phongnickchinh/sendove-box/sendlove_enclosure/breadcat/huong_dan/H02_giao_dien.png

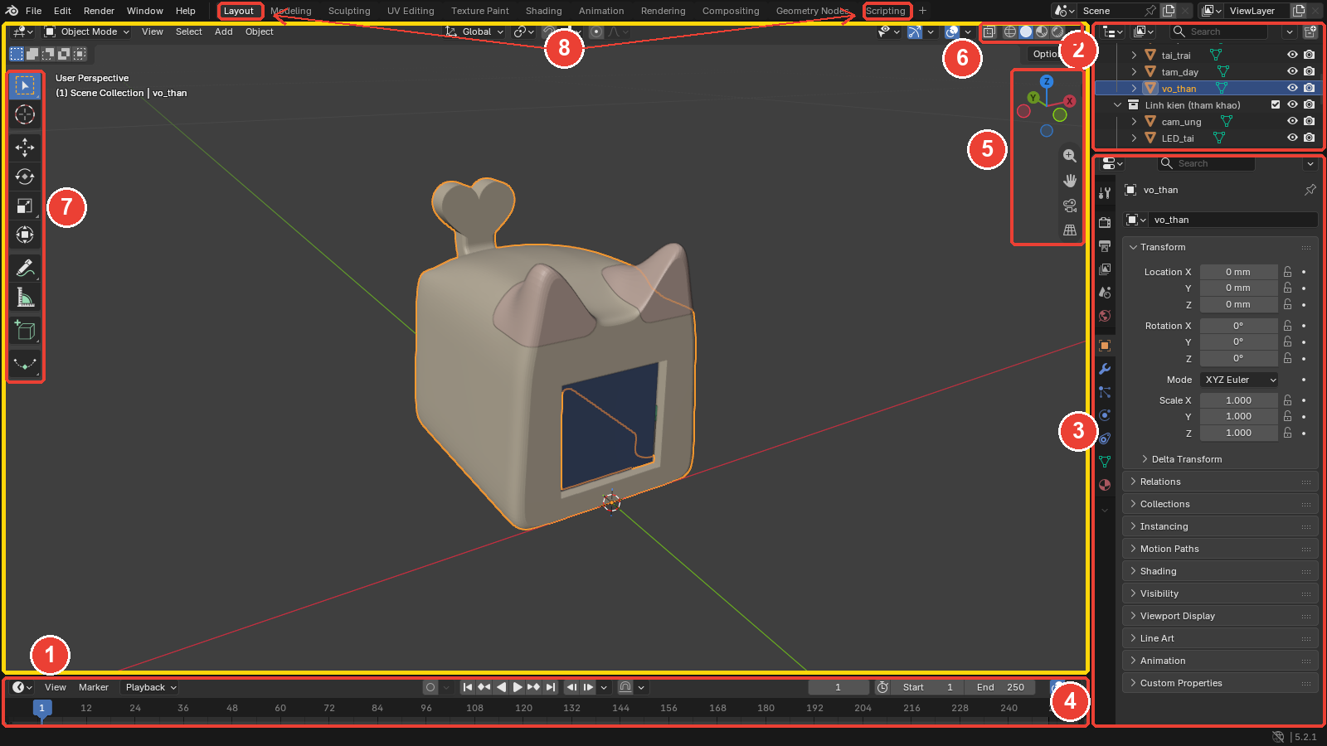
sendlove_enclosure/breadcat/huong_dan/H02_giao_dien.png
