phongnickchinh/sendove-box/sendlove_enclosure/breadcat/huong_dan/H03_gizmo.png

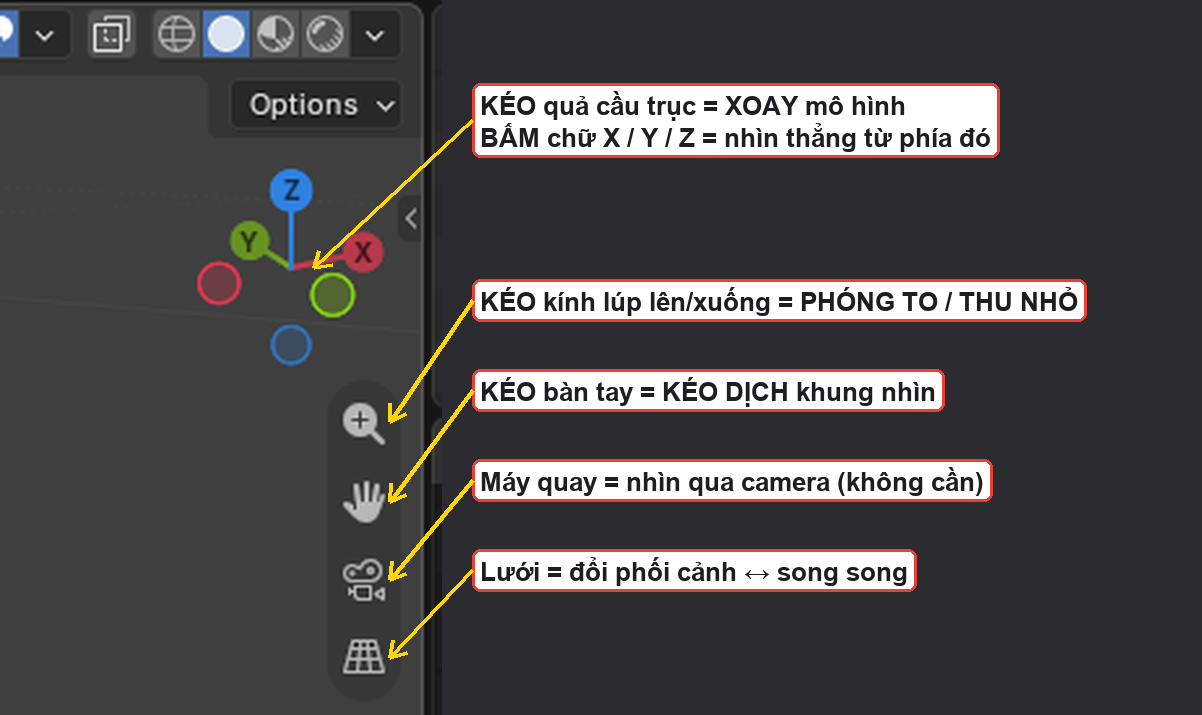
sendlove_enclosure/breadcat/huong_dan/H03_gizmo.png
