phongnickchinh/sendove-box/sendlove_enclosure/breadcat/huong_dan/H04_chuot.png

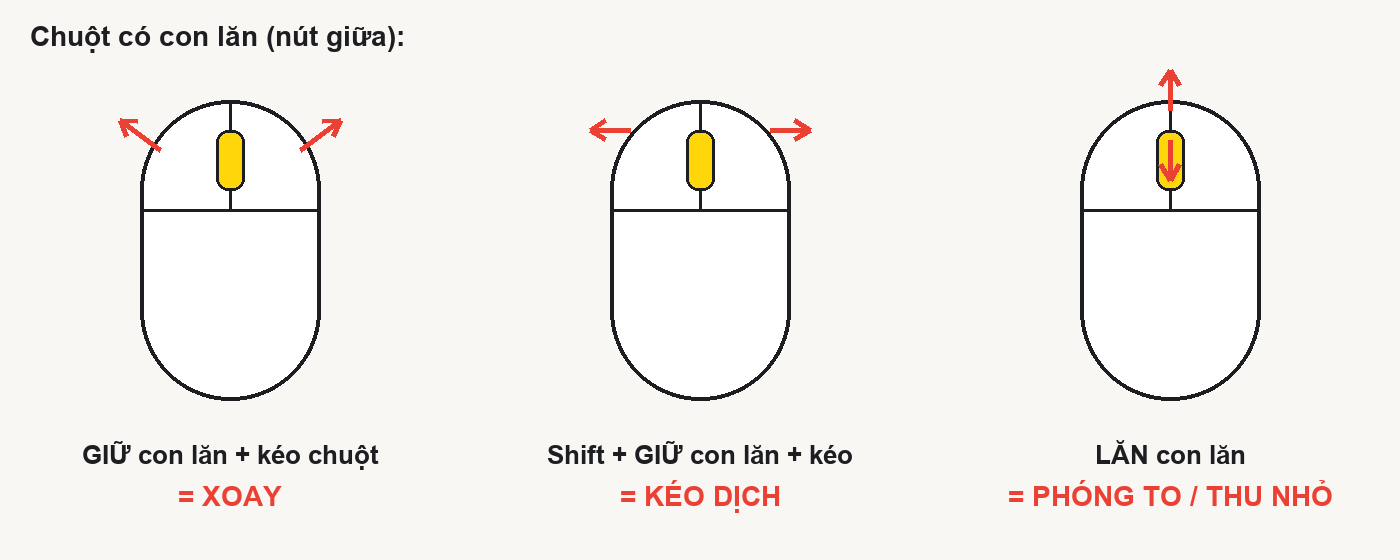
sendlove_enclosure/breadcat/huong_dan/H04_chuot.png
