phongnickchinh/sendove-box/sendlove_enclosure/breadcat/huong_dan/H05_prefs_input.png

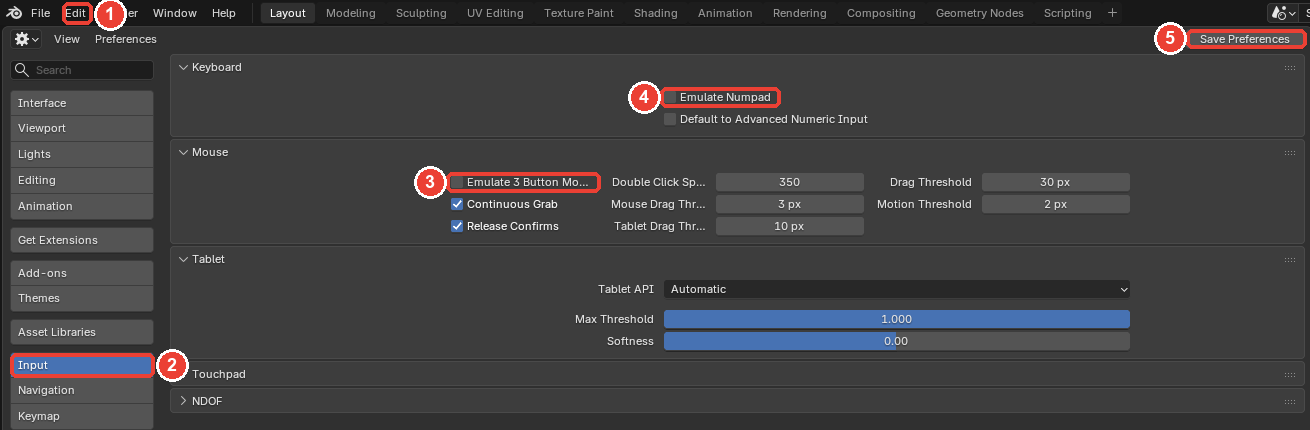
sendlove_enclosure/breadcat/huong_dan/H05_prefs_input.png
