phongnickchinh/sendove-box/sendlove_enclosure/breadcat/huong_dan/H07_menu_view.png

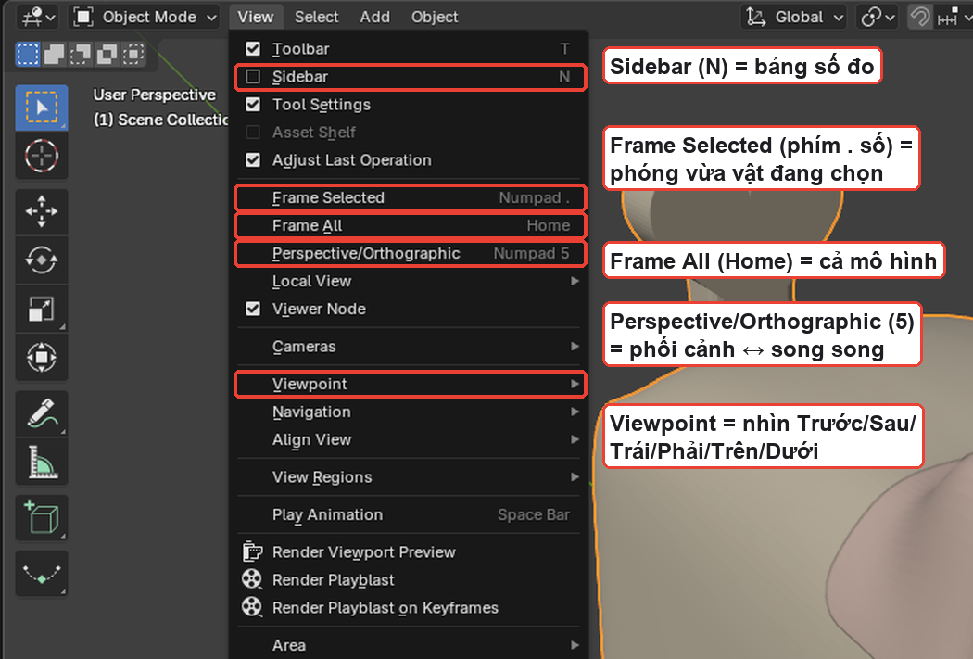
sendlove_enclosure/breadcat/huong_dan/H07_menu_view.png
