phongnickchinh/sendove-box/sendlove_enclosure/breadcat/huong_dan/H08_goc_chuan.png

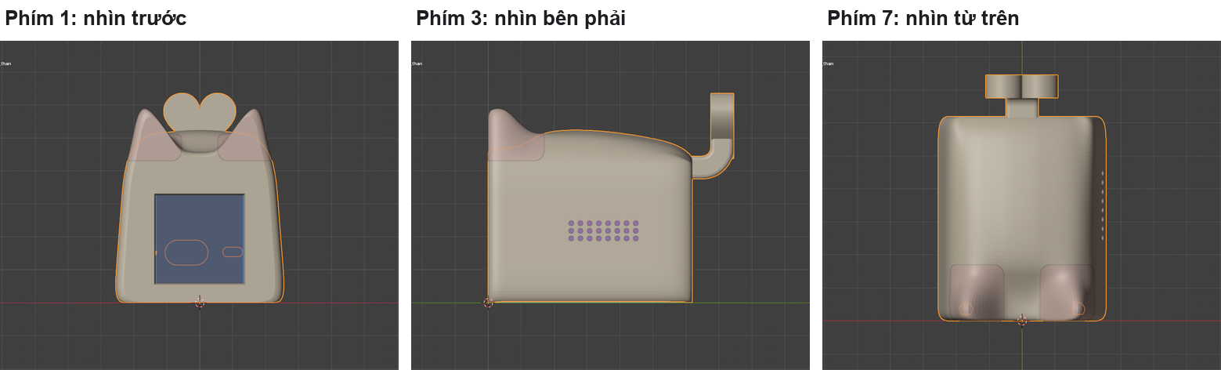
sendlove_enclosure/breadcat/huong_dan/H08_goc_chuan.png
