phongnickchinh/sendove-box/sendlove_enclosure/breadcat/huong_dan/H09_an_hien.png

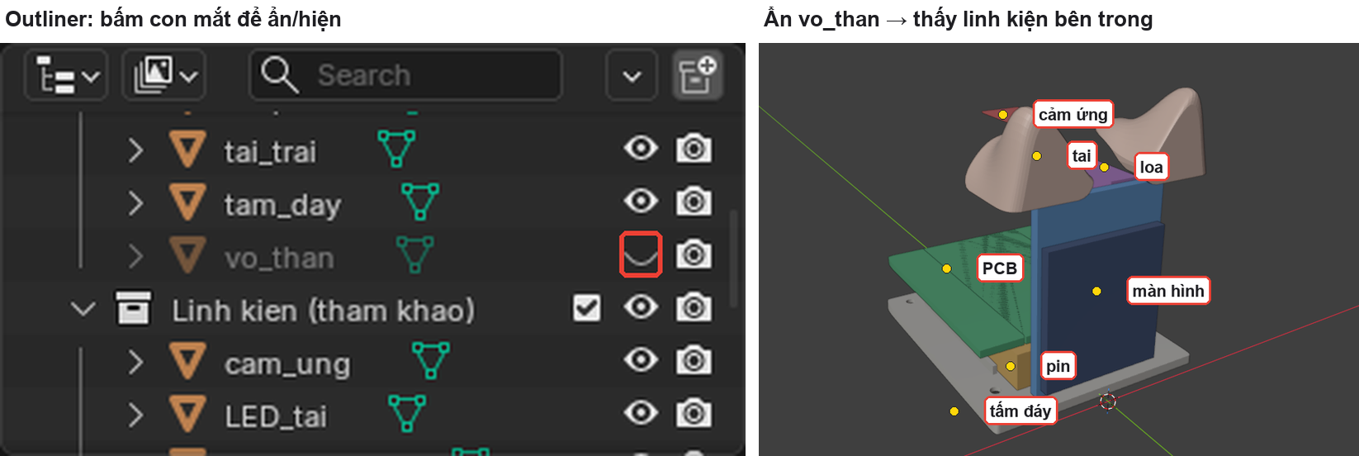
sendlove_enclosure/breadcat/huong_dan/H09_an_hien.png
