phongnickchinh/sendove-box/sendlove_enclosure/breadcat/huong_dan/H10_xray.png

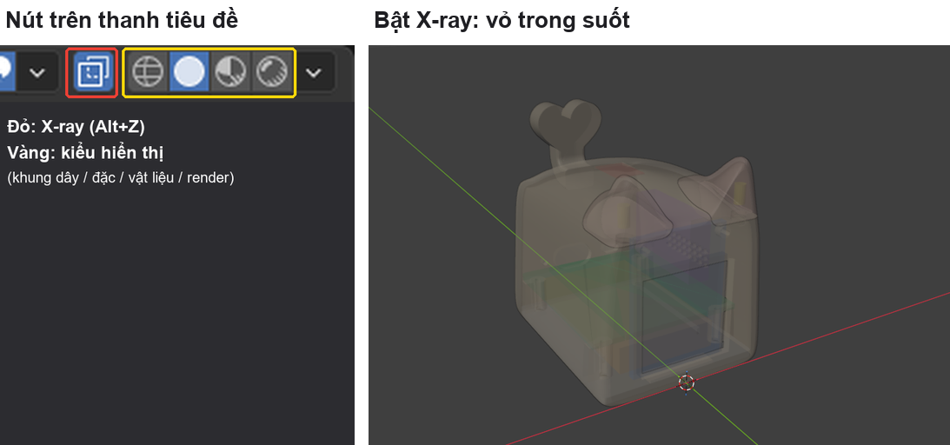
sendlove_enclosure/breadcat/huong_dan/H10_xray.png
