phongnickchinh/sendove-box/sendlove_enclosure/breadcat/huong_dan/H11_bang_n.png

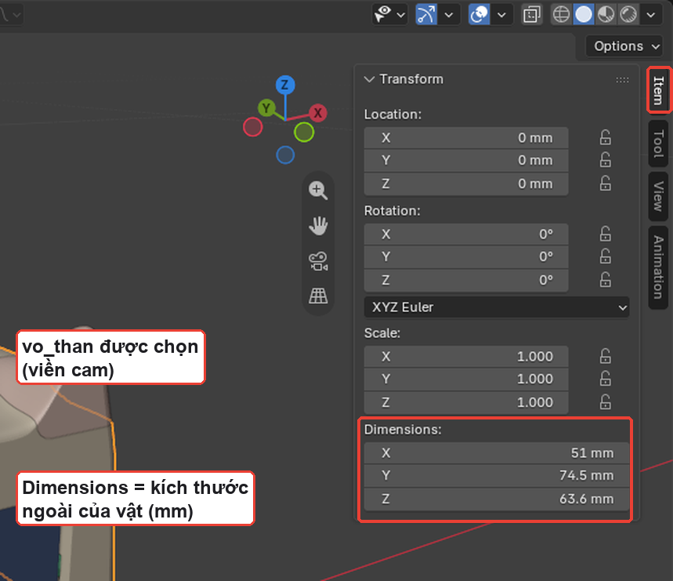
sendlove_enclosure/breadcat/huong_dan/H11_bang_n.png
