phongnickchinh/sendove-box/sendlove_enclosure/breadcat/huong_dan/H12_scripting.png

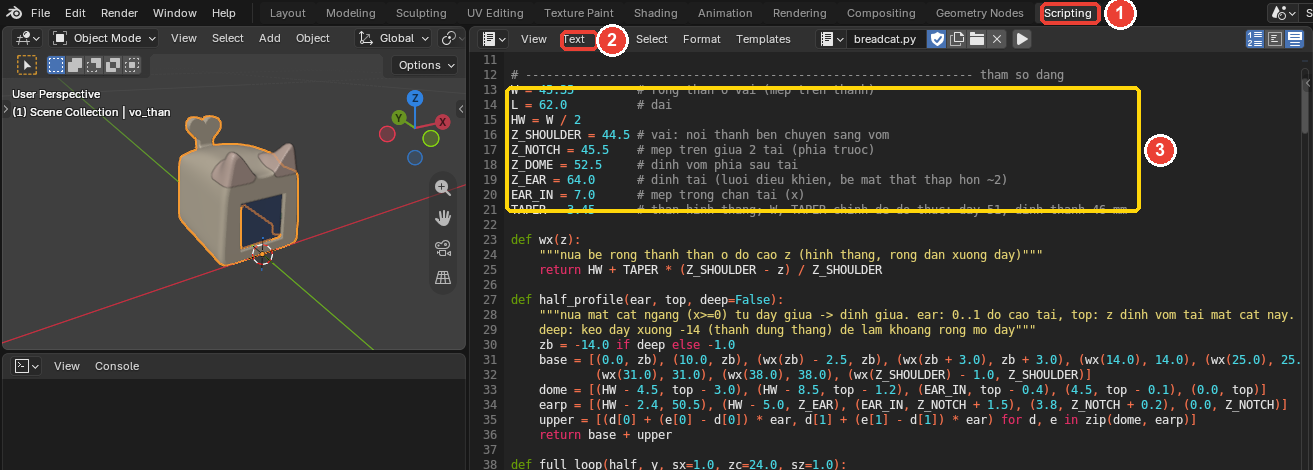
sendlove_enclosure/breadcat/huong_dan/H12_scripting.png
