phongnickchinh/sendove-box/sendlove_enclosure/breadcat/huong_dan/H12b_duoi_tim.png

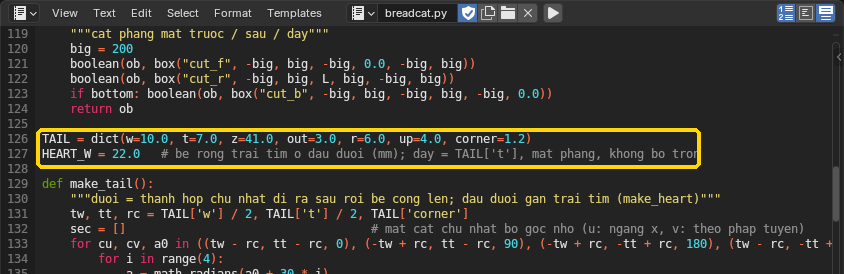
sendlove_enclosure/breadcat/huong_dan/H12b_duoi_tim.png
