phongnickchinh/sendove-box/sendlove_enclosure/breadcat/huong_dan/H12c_menu_text.png

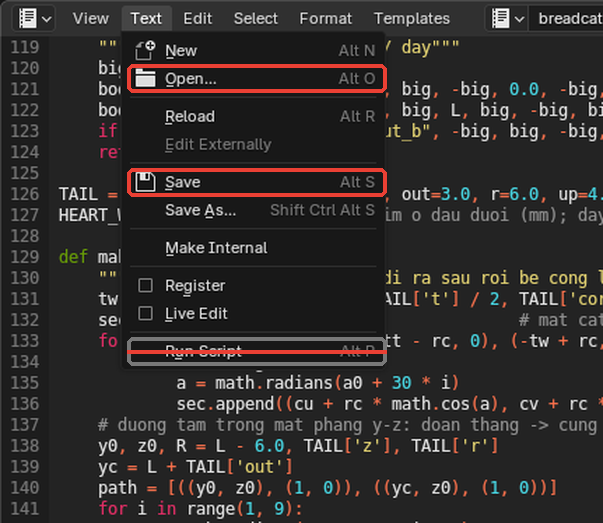
sendlove_enclosure/breadcat/huong_dan/H12c_menu_text.png
