phongnickchinh/sendove-box/sendlove_enclosure/breadcat/huong_dan/H13_menu_file.png

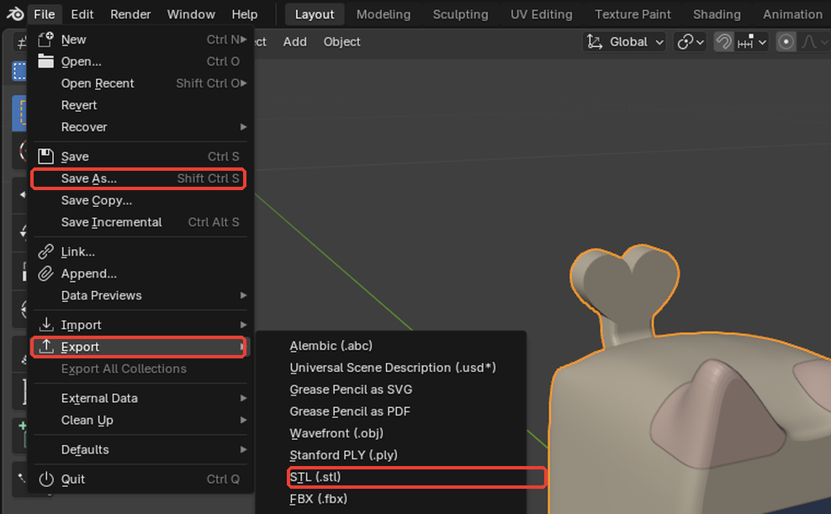
sendlove_enclosure/breadcat/huong_dan/H13_menu_file.png
