phongnickchinh/sendove-box/sendlove_enclosure/breadcat/huong_dan/H14_them_chu.png

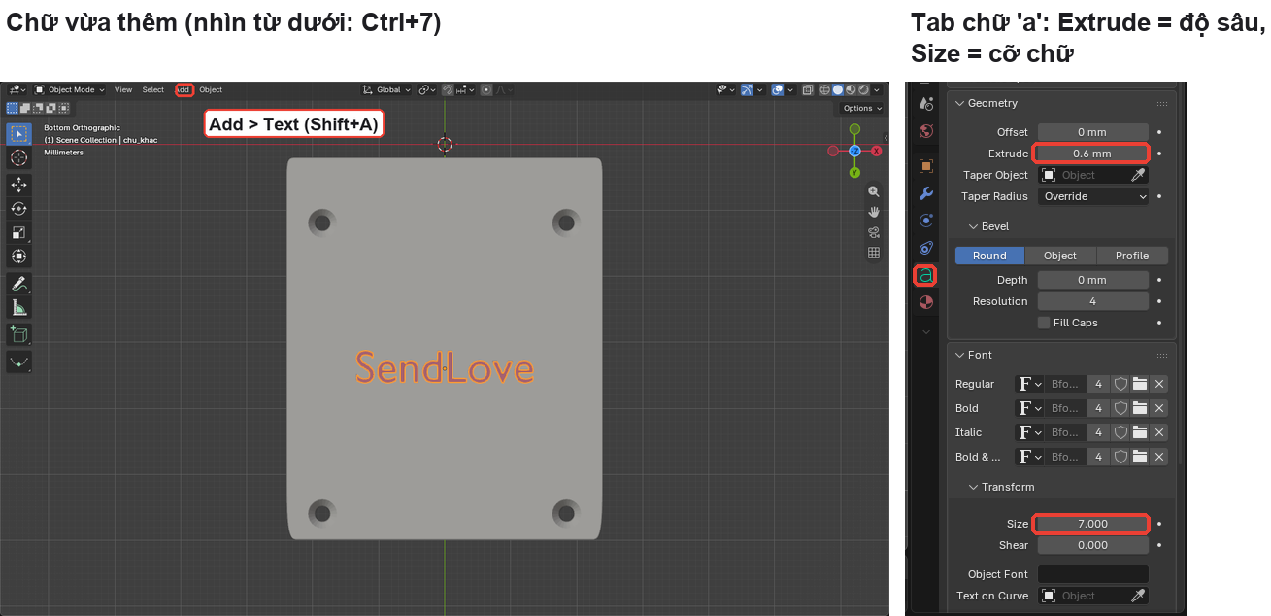
sendlove_enclosure/breadcat/huong_dan/H14_them_chu.png
