phongnickchinh/sendove-box/sendlove_enclosure/breadcat/huong_dan/H15_menu_convert.png

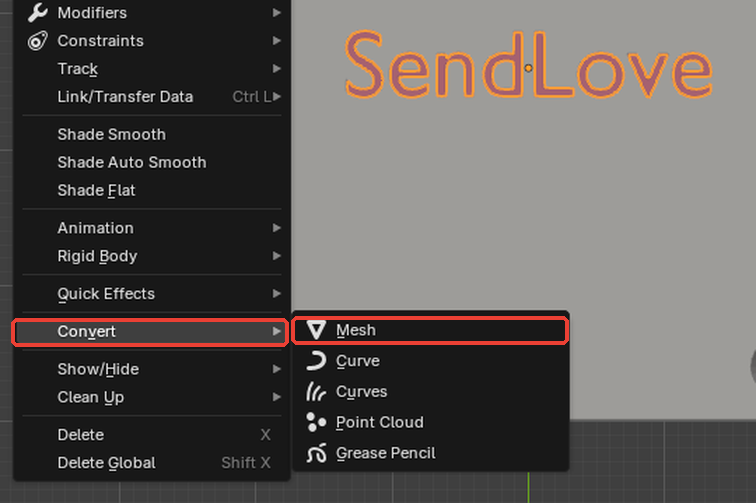
sendlove_enclosure/breadcat/huong_dan/H15_menu_convert.png
