phongnickchinh/sendove-box/sendlove_enclosure/breadcat/huong_dan/H16_boolean.png

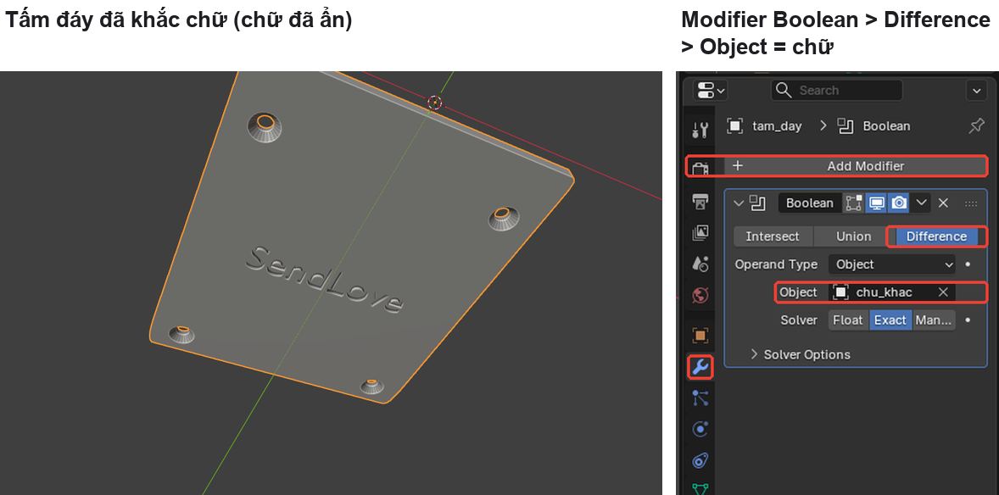
sendlove_enclosure/breadcat/huong_dan/H16_boolean.png
