phongnickchinh/sendove-box/sendlove_enclosure/breadcat/huong_dan/H17_xuat_stl.png

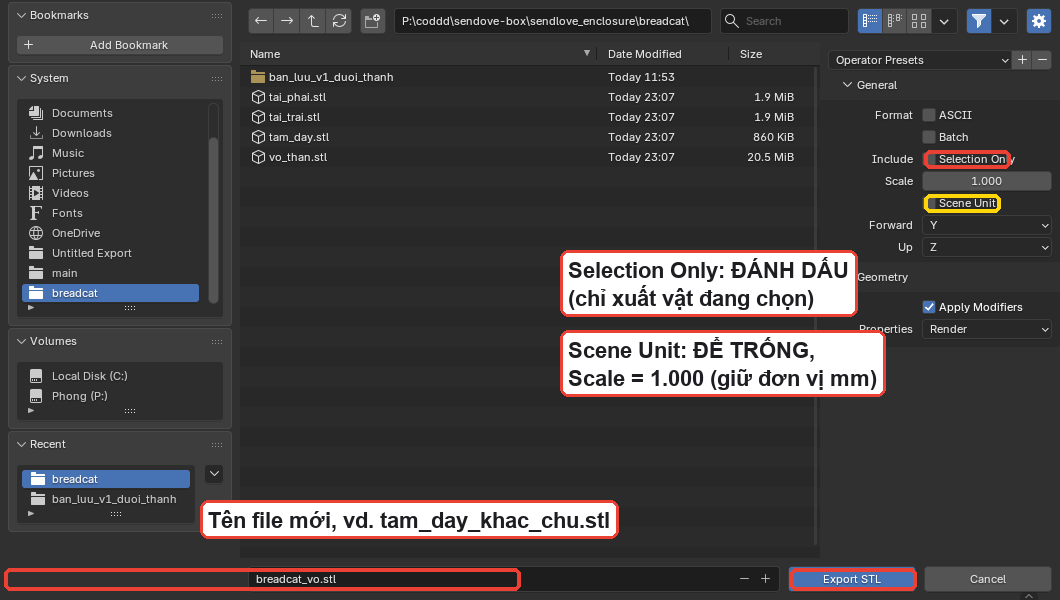
sendlove_enclosure/breadcat/huong_dan/H17_xuat_stl.png
