phongnickchinh/sendove-box/sendlove_enclosure/breadcat/huong_dan/P1_Z_EAR.png

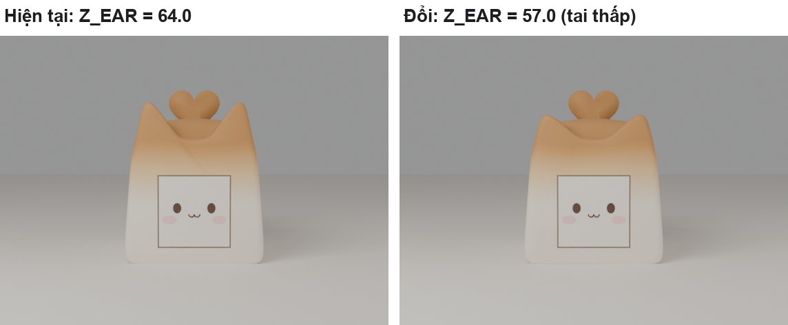
sendlove_enclosure/breadcat/huong_dan/P1_Z_EAR.png
