phongnickchinh/sendove-box/sendlove_enclosure/breadcat/huong_dan/P3_Z_DOME.png

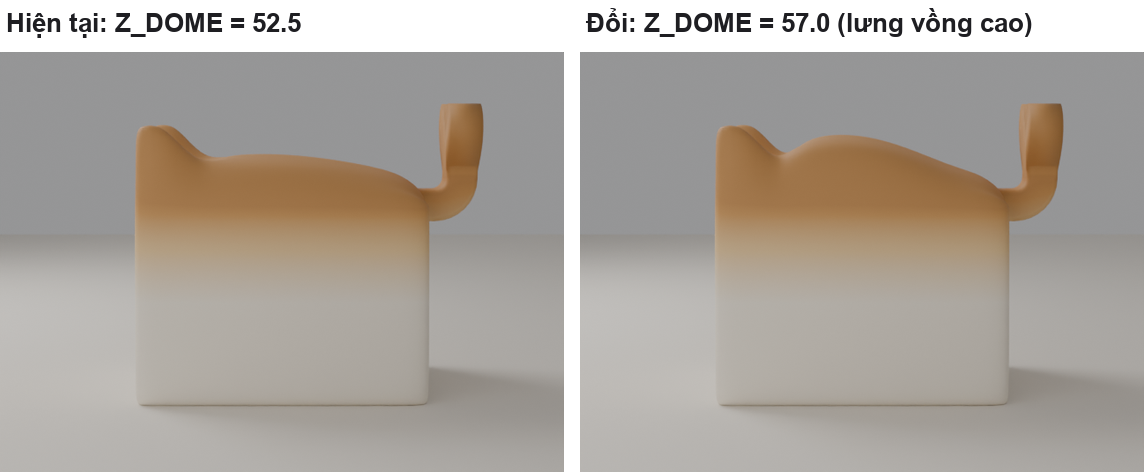
sendlove_enclosure/breadcat/huong_dan/P3_Z_DOME.png
