phongnickchinh/sendove-box/sendlove_enclosure/breadcat/huong_dan/P4_HEART_W.png

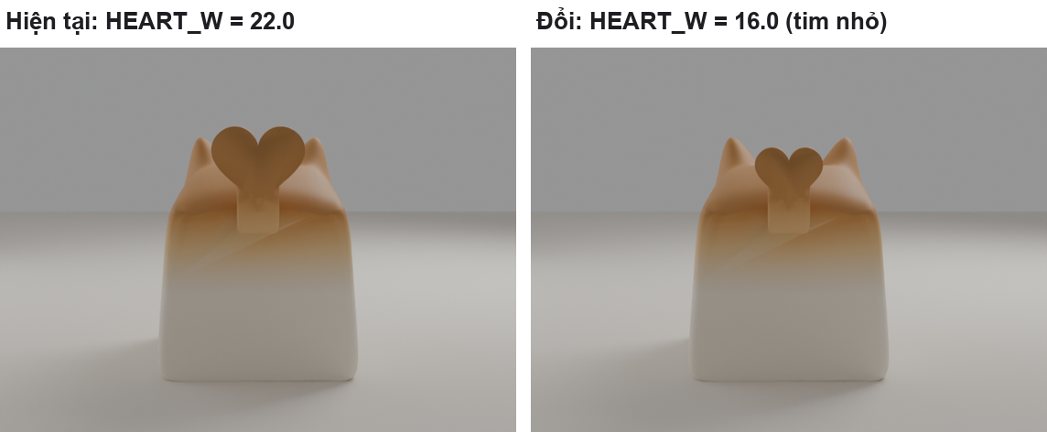
sendlove_enclosure/breadcat/huong_dan/P4_HEART_W.png
