phongnickchinh/sendove-box/sendlove_enclosure/breadcat/huong_dan/P7_L.png

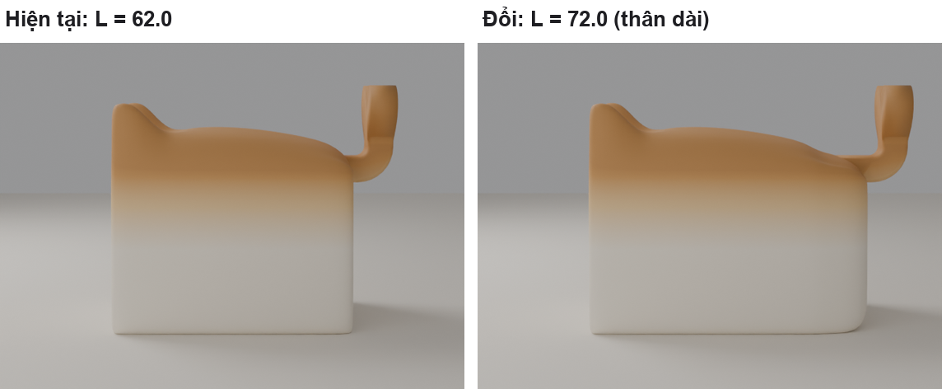
sendlove_enclosure/breadcat/huong_dan/P7_L.png
