phongnickchinh/sendove-box/sendlove_enclosure/breadcat/ky_thuat_cat_doc.png

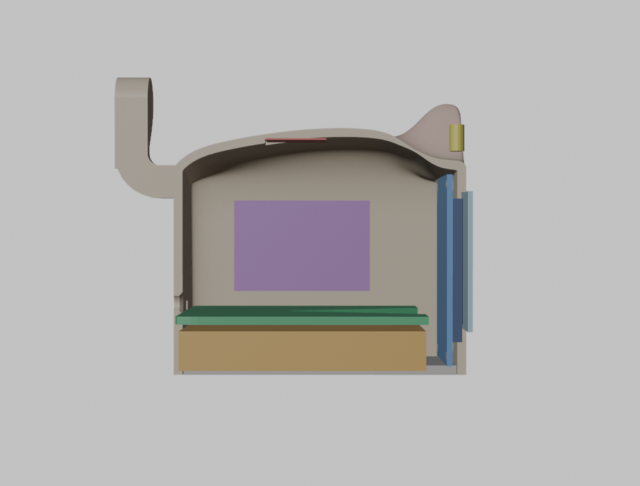
sendlove_enclosure/breadcat/ky_thuat_cat_doc.png
