phongnickchinh/sendove-box/sendlove_enclosure/breadcat/ky_thuat_day.png

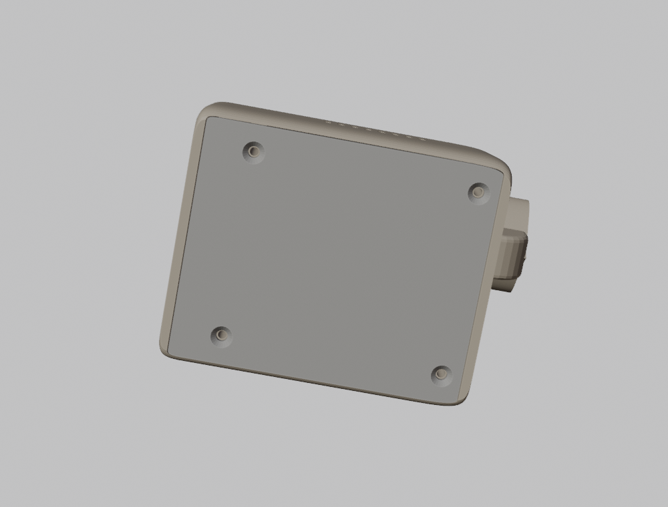
sendlove_enclosure/breadcat/ky_thuat_day.png
