phongnickchinh/sendove-box/sendlove_enclosure/breadcat/ky_thuat_mat_sau.png

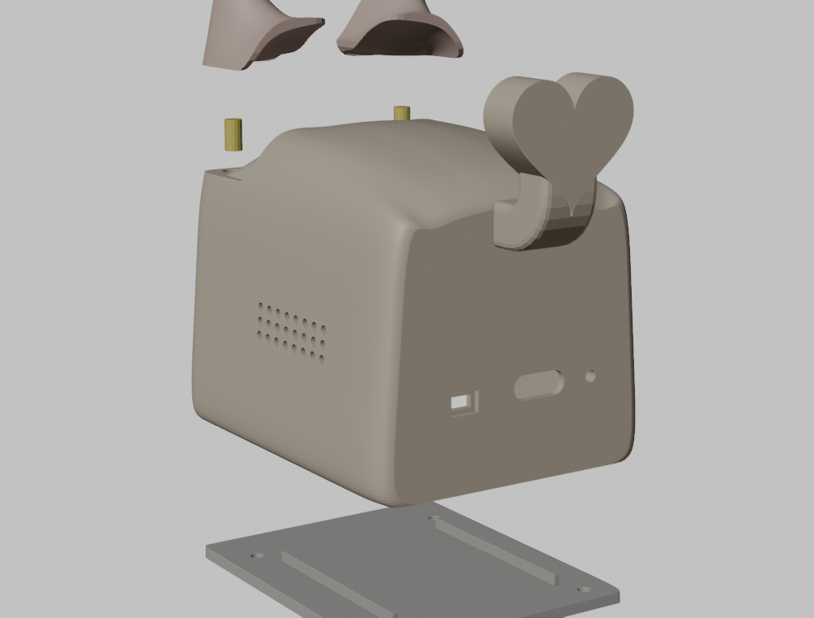
sendlove_enclosure/breadcat/ky_thuat_mat_sau.png
