phongnickchinh/sendove-box/sendlove_enclosure/breadcat/ky_thuat_no_tung.png

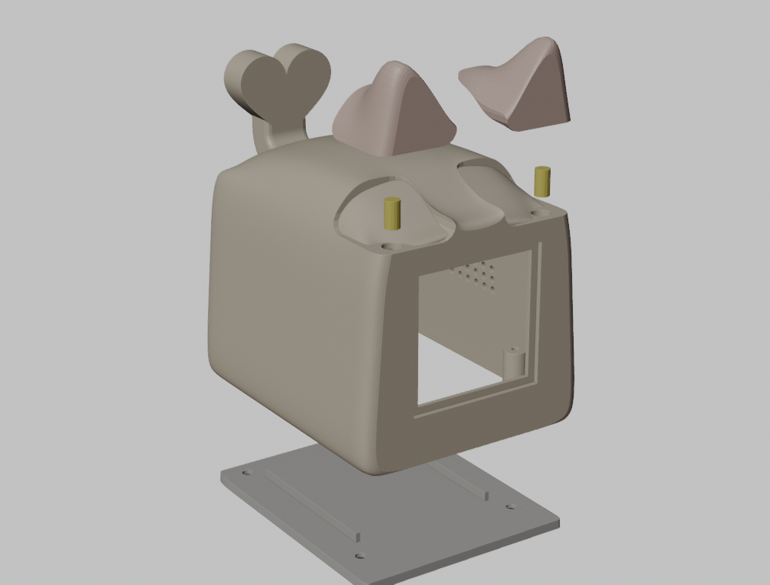
sendlove_enclosure/breadcat/ky_thuat_no_tung.png
