phongnickchinh/sendove-box/sendlove_enclosure/breadcat/man_hinh_linh_kien.png

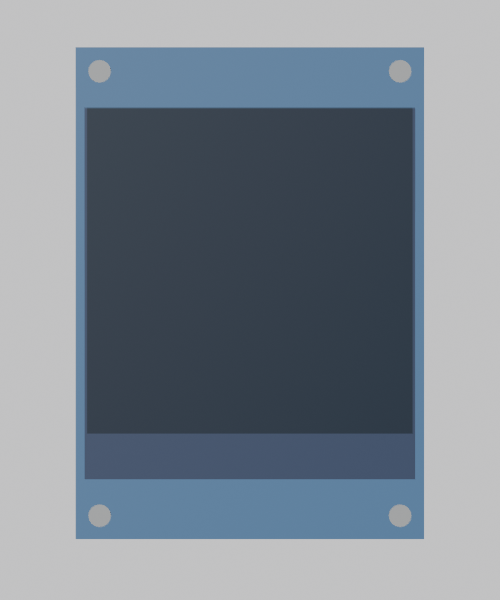
sendlove_enclosure/breadcat/man_hinh_linh_kien.png
