phongnickchinh/sendove-box/sendlove_enclosure/breadcat/shape_back.png

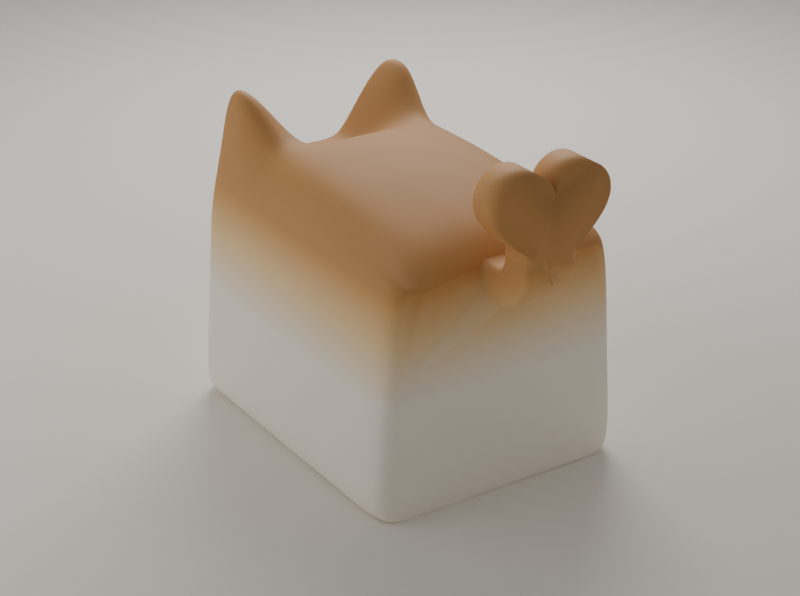
sendlove_enclosure/breadcat/shape_back.png
