phongnickchinh/sendove-box/sendlove_enclosure/breadcat/shape_front.png

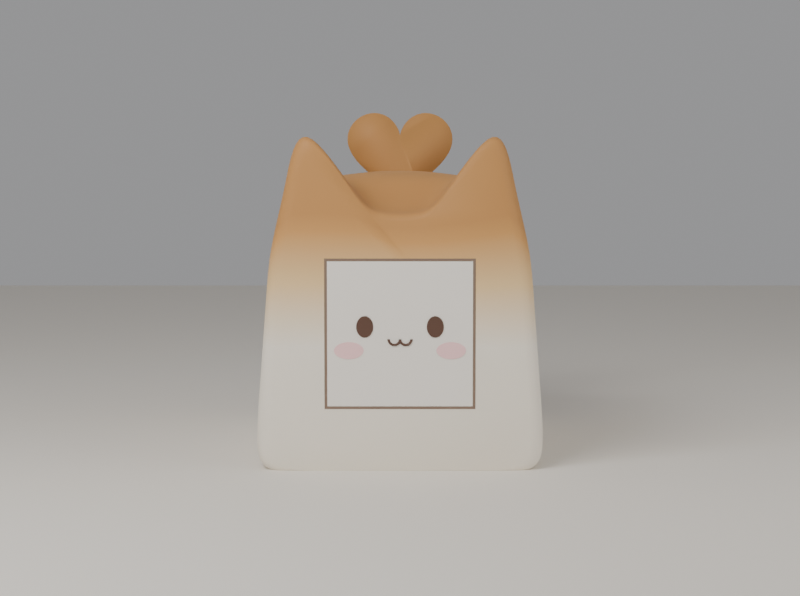
sendlove_enclosure/breadcat/shape_front.png
