phongnickchinh/sendove-box/sendlove_enclosure/breadcat/shape_rear.png

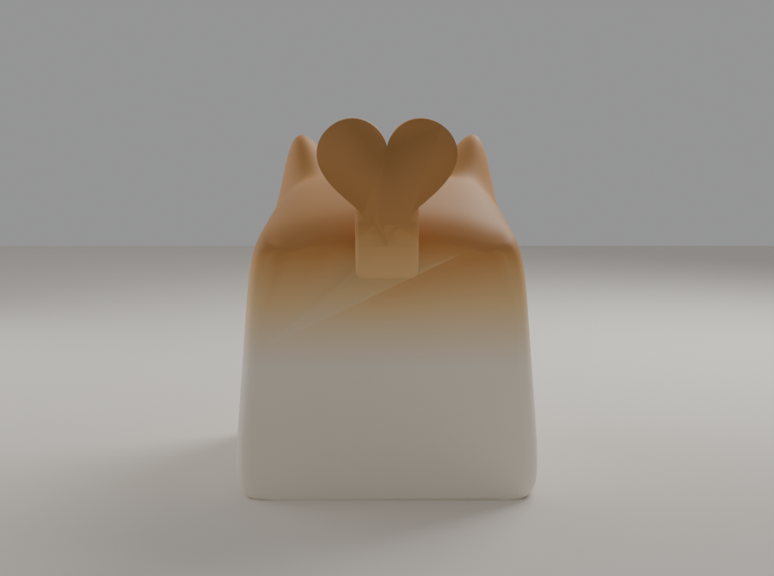
sendlove_enclosure/breadcat/shape_rear.png
