phongnickchinh/sendove-box/sendlove_enclosure/breadcat/shape_side.png

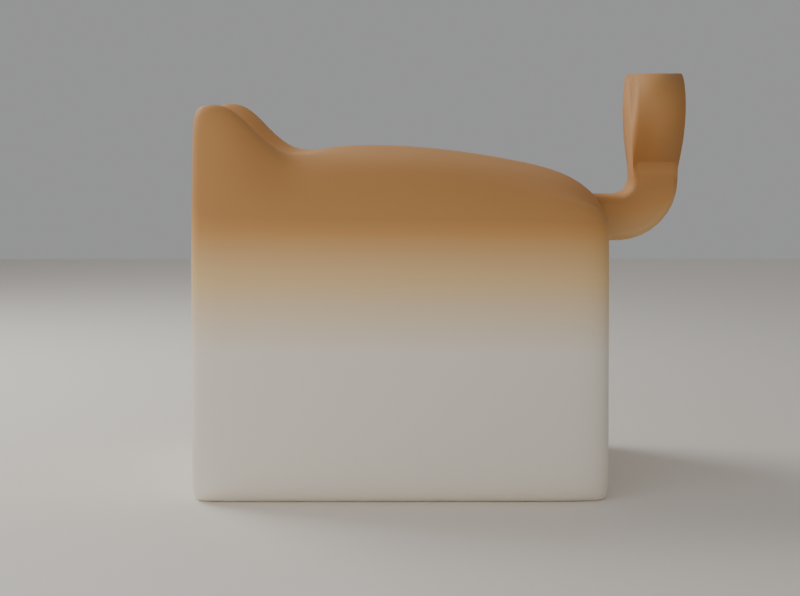
sendlove_enclosure/breadcat/shape_side.png
