phongnickchinh/sendove-box/sendlove_enclosure/breadcat/shape_v34.png

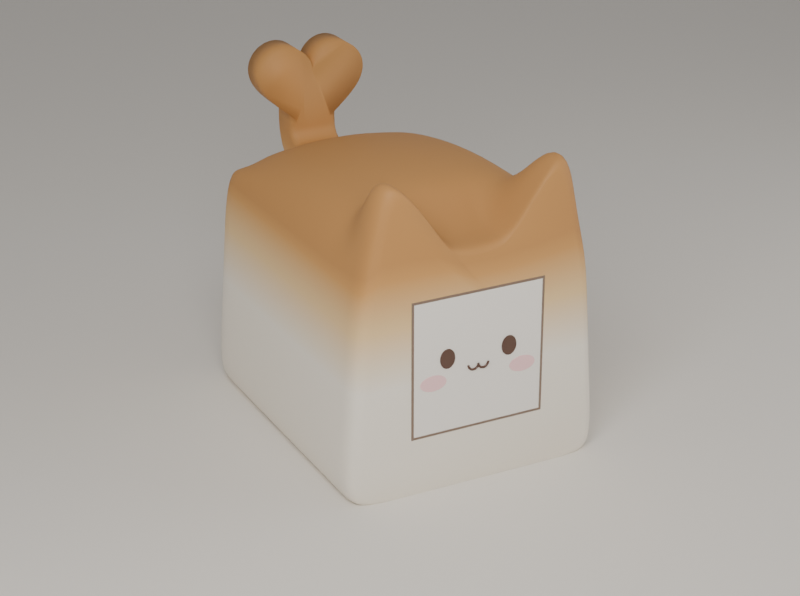
sendlove_enclosure/breadcat/shape_v34.png
