phongnickchinh/sendove-box/sendlove_firmware/include/CustomBatteryIcons.h

#ifndef CUSTOM_BATTERY_ICONS_H
#define CUSTOM_BATTERY_ICONS_H

#include <pgmspace.h>
#include <Arduino.h>

// Battery Icon Set (5 frames: 0..4, size: 75x16 RGB565)

const uint16_t battery_icon_state_0[1200] PROGMEM = {
  0x0001, 0x0001, 0xE2AC, 0xF8A5, 0xF907, 0xF907, 0xF928, 0x0001, 0x0001, 0x0001, 0x0001, 0xF907, 
  0xF907, 0xF907, 0xF927, 0xC8C5, 0x0001, 0x0001, 0x0001, 0x0001, 0x0001, 0xE2AC, 0xF8A5, 0xF907, 
  0xF907, 0xF928, 0x0001, 0x0001, 0x0001, 0x0001, 0xF907, 0xF907, 0xF907, 0xF927, 0xC8C5, 0x0001, 
  0x0001, 0x0001, 0x0001, 0x0001, 0xE2AC, 0xF8A5, 0xF907, 0xF907, 0xF928, 0x0001, 0x0001, 0x0001, 
  0x0001, 0xF907, 0xF907, 0xF907, 0xF927, 0xC8C5, 0x0001, 0x0001, 0x0001, 0x0001, 0x0001, 0xE2AC, 
  0xF8A5, 0xF907, 0xF907, 0xF928, 0x0001, 0x0001, 0x0001, 0x0001, 0xF907, 0xF907, 0xF907, 0xF927, 
  0xC8C5, 0x0001, 0x0001, 0x0001, 0xE147, 0xA8A4, 0x0001, 0x0001, 0x0001, 0x0001, 0xE907, 0x0001, 
  0x0001, 0xE8C6, 0x0001, 0x0001, 0x0001, 0x0001, 0x0001, 0xF1CA, 0x0001, 0x0001, 0x0001, 0xE147, 
  0xA8A4, 0x0001, 0x0001, 0x0001, 0x0001, 0xE907, 0x0001, 0x0001, 0xE8C6, 0x0001, 0x0001, 0x0001, 
  0x0001, 0x0001, 0xF1CA, 0x0001, 0x0001, 0x0001, 0xE147, 0xA8A4, 0x0001, 0x0001, 0x0001, 0x0001, 
  0xE907, 0x0001, 0x0001, 0xE8C6, 0x0001, 0x0001, 0x0001, 0x0001, 0x0001, 0xF1CA, 0x0001, 0x0001, 
  0x0001, 0xE147, 0xA8A4, 0x0001, 0x0001, 0x0001, 0x0001, 0xE907, 0x0001, 0x0001, 0xE8C6, 0x0001, 
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
    battery_icon_state_2,
    battery_icon_state_3,
    battery_icon_state_4,
};

static constexpr uint8_t BATTERY_ICON_WIDTH = 75;
static constexpr uint8_t BATTERY_ICON_HEIGHT = 16;
static constexpr uint16_t BATTERY_TRANSPARENT_COLOR = 0x0001;

#endif // CUSTOM_BATTERY_ICONS_H
