phongnickchinh/sendove-box/sendlove_firmware/include/firebase_root_ca.h

#ifndef FIREBASE_ROOT_CA_H
#define FIREBASE_ROOT_CA_H

#include <pgmspace.h>
// Root CAs for HTTPS to Firebase. NOT a secret (unlike config_secrets.h).
//
// Chains measured with openssl s_client (2026-09-03); BOTH roots are required:
//   iot-app-839a2.asia-southeast1.firebasedatabase.app -> GTS Root R1 (RSA)
//   firebasestorage.googleapis.com                     -> GTS Root R4 (ECC)
// These are the SELF-SIGNED roots from https://pki.goog/repo/certs/ (expire
// 2036-06-22), NOT the GlobalSign cross-signed ones in the server chain (2028-01-28).
//
// SHA-256 fingerprints:
//   GTS Root R1: D9:47:43:2A:BD:E7:B7:FA:90:FC:2E:6B:59:10:1B:12:
//                80:E0:E1:C7:E4:E4:0F:A3:C6:88:7F:FF:57:A7:F4:CF
//   GTS Root R4: 34:9D:FA:40:58:C5:E2:63:12:3B:39:8A:E7:95:57:3C:
//                4E:13:13:C8:3F:E6:8F:93:55:6C:D5:E8:03:1B:3C:7D
//
// Re-check:
//   curl -o gtsr1.pem https://pki.goog/repo/certs/gtsr1.pem
//   openssl x509 -in gtsr1.pem -noout -subject -enddate -fingerprint -sha256
//
// If Google changes roots the handshake fails ("[NET] tls: ..." shows a verify
// error) and the box needs new firmware. Both PEMs live in one string, which
// mbedTLS parses as a chain list.

static const char FIREBASE_ROOT_CA[] PROGMEM =
"-----BEGIN CERTIFICATE-----\n"
"MIIFVzCCAz+gAwIBAgINAgPlk28xsBNJiGuiFzANBgkqhkiG9w0BAQwFADBHMQsw\n"
"CQYDVQQGEwJVUzEiMCAGA1UEChMZR29vZ2xlIFRydXN0IFNlcnZpY2VzIExMQzEU\n"
"MBIGA1UEAxMLR1RTIFJvb3QgUjEwHhcNMTYwNjIyMDAwMDAwWhcNMzYwNjIyMDAw\n"
"MDAwWjBHMQswCQYDVQQGEwJVUzEiMCAGA1UEChMZR29vZ2xlIFRydXN0IFNlcnZp\n"
"Y2VzIExMQzEUMBIGA1UEAxMLR1RTIFJvb3QgUjEwggIiMA0GCSqGSIb3DQEBAQUA\n"
"A4ICDwAwggIKAoICAQC2EQKLHuOhd5s73L+UPreVp0A8of2C+X0yBoJx9vaMf/vo\n"
"27xqLpeXo4xL+Sv2sfnOhB2x+cWX3u+58qPpvBKJXqeqUqv4IyfLpLGcY9vXmX7w\n"
"Cl7raKb0xlpHDU0QM+NOsROjyBhsS+z8CZDfnWQpJSMHobTSPS5g4M/SCYe7zUjw\n"
"TcLCeoiKu7rPWRnWr4+wB7CeMfGCwcDfLqZtbBkOtdh+JhpFAz2weaSUKK0Pfybl\n"
"qAj+lug8aJRT7oM6iCsVlgmy4HqMLnXWnOunVmSPlk9orj2XwoSPwLxAwAtcvfaH\n"
"szVsrBhQf4TgTM2S0yDpM7xSma8ytSmzJSq0SPly4cpk9+aCEI3oncKKiPo4Zor8\n"
"Y/kB+Xj9e1x3+naH+uzfsQ55lVe0vSbv1gHR6xYKu44LtcXFilWr06zqkUspzBmk\n"
"MiVOKvFlRNACzqrOSbTqn3yDsEB750Orp2yjj32JgfpMpf/VjsPOS+C12LOORc92\n"
"wO1AK/1TD7Cn1TsNsYqiA94xrcx36m97PtbfkSIS5r762DL8EGMUUXLeXdYWk70p\n"
"aDPvOmbsB4om3xPXV2V4J95eSRQAogB/mqghtqmxlbCluQ0WEdrHbEg8QOB+DVrN\n"
"VjzRlwW5y0vtOUucxD/SVRNuJLDWcfr0wbrM7Rv1/oFB2ACYPTrIrnqYNxgFlQID\n"
"AQABo0IwQDAOBgNVHQ8BAf8EBAMCAYYwDwYDVR0TAQH/BAUwAwEB/zAdBgNVHQ4E\n"
"FgQU5K8rJnEaK0gnhS9SZizv8IkTcT4wDQYJKoZIhvcNAQEMBQADggIBAJ+qQibb\n"
"C5u+/x6Wki4+omVKapi6Ist9wTrYggoGxval3sBOh2Z5ofmmWJyq+bXmYOfg6LEe\n"
"QkEzCzc9zolwFcq1JKjPa7XSQCGYzyI0zzvFIoTgxQ6KfF2I5DUkzps+GlQebtuy\n"
"h6f88/qBVRRiClmpIgUxPoLW7ttXNLwzldMXG+gnoot7TiYaelpkttGsN/H9oPM4\n"
"7HLwEXWdyzRSjeZ2axfG34arJ45JK3VmgRAhpuo+9K4l/3wV3s6MJT/KYnAK9y8J\n"
"ZgfIPxz88NtFMN9iiMG1D53Dn0reWVlHxYciNuaCp+0KueIHoI17eko8cdLiA6Ef\n"
"MgfdG+RCzgwARWGAtQsgWSl4vflVy2PFPEz0tv/bal8xa5meLMFrUKTX5hgUvYU/\n"
"Z6tGn6D/Qqc6f1zLXbBwHSs09dR2CQzreExZBfMzQsNhFRAbd03OIozUhfJFfbdT\n"
"6u9AWpQKXCBfTkBdYiJ23//OYb2MI3jSNwLgjt7RETeJ9r/tSQdirpLsQBqvFAnZ\n"
"0E6yove+7u7Y/9waLd64NnHi/Hm3lCXRSHNboTXns5lndcEZOitHTtNCjv0xyBZm\n"
"2tIMPNuzjsmhDYAPexZ3FL//2wmUspO8IFgV6dtxQ/PeEMMA3KgqlbbC1j+Qa3bb\n"
"bP6MvPJwNQzcmRk13NfIRmPVNnGuV/u3gm3c\n"
"-----END CERTIFICATE-----\n"
"-----BEGIN CERTIFICATE-----\n"
"MIICCTCCAY6gAwIBAgINAgPlwGjvYxqccpBQUjAKBggqhkjOPQQDAzBHMQswCQYD\n"
"VQQGEwJVUzEiMCAGA1UEChMZR29vZ2xlIFRydXN0IFNlcnZpY2VzIExMQzEUMBIG\n"
"A1UEAxMLR1RTIFJvb3QgUjQwHhcNMTYwNjIyMDAwMDAwWhcNMzYwNjIyMDAwMDAw\n"
"WjBHMQswCQYDVQQGEwJVUzEiMCAGA1UEChMZR29vZ2xlIFRydXN0IFNlcnZpY2Vz\n"
"IExMQzEUMBIGA1UEAxMLR1RTIFJvb3QgUjQwdjAQBgcqhkjOPQIBBgUrgQQAIgNi\n"
"AATzdHOnaItgrkO4NcWBMHtLSZ37wWHO5t5GvWvVYRg1rkDdc/eJkTBa6zzuhXyi\n"
"QHY7qca4R9gq55KRanPpsXI5nymfopjTX15YhmUPoYRlBtHci8nHc8iMai/lxKvR\n"
"HYqjQjBAMA4GA1UdDwEB/wQEAwIBhjAPBgNVHRMBAf8EBTADAQH/MB0GA1UdDgQW\n"
"BBSATNbrdP9JNqPV2Py1PsVq8JQdjDAKBggqhkjOPQQDAwNpADBmAjEA6ED/g94D\n"
"9J+uHXqnLrmvT/aDHQ4thQEd0dlq7A/Cr8deVl5c1RxYIigL9zC2L7F8AjEA8GE8\n"
"p/SgguMh1YQdc4acLa/KNJvxn7kjNuK8YAOdgLOaVsjh4rsUecrNIdSUtUlD\n"
"-----END CERTIFICATE-----\n"
;

#endif // FIREBASE_ROOT_CA_H
