phongnickchinh/sendove-box/sendlove_firmware/include/CustomWifiIcons.h

#ifndef CUSTOM_WIFI_ICONS_H
#define CUSTOM_WIFI_ICONS_H

#include <pgmspace.h>
#include <Arduino.h>

// Wi-Fi Icon Set (5 frames: 0..4 bars, size: 24x24)

const uint8_t wifi_icon_bar_0[] PROGMEM = {
  0x00, 0x00, 0x00, 0x00, 0x00, 0x00, 0x00, 0x00, 0x00, 0x00, 0x00, 0x00, 
  0x00, 0x00, 0x00, 0x00, 0x00, 0x00, 0x00, 0x00, 0x00, 0x00, 0x00, 0x00, 
  0x00, 0x00, 0x00, 0x00, 0x00, 0x00, 0x00, 0x00, 0x00, 0x00, 0x00, 0x00, 
  0x00, 0x00, 0x00, 0x00, 0x00, 0x00, 0x00, 0x00, 0x00, 0x00, 0x00, 0x00, 
  0x00, 0x00, 0x00, 0x00, 0x00, 0x00, 0x00, 0x00, 0x00, 0x00, 0x18, 0x00, 
  0x00, 0x18, 0x00, 0x00, 0x00, 0x00, 0x00, 0x00, 0x00, 0x00, 0x00, 0x00, 
};

const uint8_t wifi_icon_bar_1[] PROGMEM = {
  0x00, 0x00, 0x00, 0x00, 0x00, 0x00, 0x00, 0x00, 0x00, 0x00, 0x00, 0x00, 
  0x00, 0x00, 0x00, 0x00, 0x00, 0x00, 0x00, 0x00, 0x00, 0x00, 0x00, 0x00, 
  0x00, 0x00, 0x00, 0x00, 0x00, 0x00, 0x00, 0x00, 0x00, 0x00, 0x00, 0x00, 
  0x00, 0x00, 0x00, 0x00, 0x00, 0x00, 0x00, 0x00, 0x00, 0x00, 0x00, 0x00, 
  0x00, 0x00, 0x00, 0x00, 0x18, 0x00, 0x00, 0x7E, 0x00, 0x00, 0x7E, 0x00, 
  0x00, 0x7E, 0x00, 0x00, 0x3C, 0x00, 0x00, 0x18, 0x00, 0x00, 0x18, 0x00, 
};

const uint8_t wifi_icon_bar_2[] PROGMEM = {
  0x00, 0x00, 0x00, 0x00, 0x00, 0x00, 0x00, 0x00, 0x00, 0x00, 0x00, 0x00, 
  0x00, 0x00, 0x00, 0x00, 0x00, 0x00, 0x00, 0x00, 0x00, 0x00, 0x00, 0x00, 
  0x00, 0x00, 0x00, 0x60, 0xFF, 0x06, 0x01, 0xFF, 0x80, 0x03, 0xFF, 0xE0, 
  0x07, 0xFF, 0xF0, 0x0F, 0xC3, 0xF0, 0x07, 0x00, 0xE0, 0x02, 0x00, 0x40, 
  0x00, 0x00, 0x00, 0x00, 0x18, 0x00, 0x00, 0x7E, 0x00, 0x00, 0x7E, 0x00, 
  0x00, 0x7E, 0x00, 0x00, 0x3C, 0x00, 0x00, 0x18, 0x00, 0x00, 0x18, 0x00, 
};

const uint8_t wifi_icon_bar_3[] PROGMEM = {
  0x00, 0x00, 0x00, 0x00, 0x00, 0x00, 0x00, 0x00, 0x00, 0x00, 0x00, 0x00, 
  0x3F, 0xFF, 0xFC, 0x7F, 0x00, 0xFE, 0xFC, 0x00, 0x3F, 0xF8, 0x00, 0x1F, 
  0x70, 0x00, 0x0E, 0x60, 0xFF, 0x06, 0x01, 0xFF, 0x80, 0x03, 0xFF, 0xE0, 
  0x07, 0xFF, 0xF0, 0x0F, 0xC3, 0xF0, 0x07, 0x00, 0xE0, 0x02, 0x00, 0x40, 
  0x00, 0x00, 0x00, 0x00, 0x18, 0x00, 0x00, 0x7E, 0x00, 0x00, 0x7E, 0x00, 
  0x00, 0x7E, 0x00, 0x00, 0x3C, 0x00, 0x00, 0x18, 0x00, 0x00, 0x18, 0x00, 
};

const uint8_t wifi_icon_bar_4[] PROGMEM = {
  0x00, 0xFF, 0x00, 0x03, 0xFF, 0xC0, 0x0F, 0xFF, 0xF0, 0x1F, 0xFF, 0xF8, 
  0x3F, 0xFF, 0xFC, 0x7F, 0x00, 0xFE, 0xFC, 0x00, 0x3F, 0xF8, 0x00, 0x1F, 
  0x70, 0x00, 0x0E, 0x60, 0xFF, 0x06, 0x01, 0xFF, 0x80, 0x03, 0xFF, 0xE0, 
  0x07, 0xFF, 0xF0, 0x0F, 0xC3, 0xF0, 0x07, 0x00, 0xE0, 0x02, 0x00, 0x40, 
  0x00, 0x00, 0x00, 0x00, 0x18, 0x00, 0x00, 0x7E, 0x00, 0x00, 0x7E, 0x00, 
  0x00, 0x7E, 0x00, 0x00, 0x3C, 0x00, 0x00, 0x18, 0x00, 0x00, 0x18, 0x00, 
};

// Pointer array for 5 wifi levels (0..4)
const uint8_t* const WIFI_ICONS[5] PROGMEM = {
    wifi_icon_bar_0,
    wifi_icon_bar_1,
    wifi_icon_bar_2,
    wifi_icon_bar_3,
    wifi_icon_bar_4,
};

static constexpr uint8_t WIFI_ICON_WIDTH = 24;
static constexpr uint8_t WIFI_ICON_HEIGHT = 24;

#endif // CUSTOM_WIFI_ICONS_H
